no3z/ScratchTJ/software/player.h

/*
 * Copyright (C) 2018 Mark Hills <mark@xwax.org>
 *
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
 */

#ifndef PLAYER_H
#define PLAYER_H

#include <stdbool.h>
#include <stdio.h>
#include <stdlib.h>

#include "spin.h"
#include "track.h"

#define PLAYER_CHANNELS 2

// How many samples each beep stage lasts
#define BEEPSPEED 4800

#define BEEP_NONE -1
#define BEEP_RECORDINGSTART 0
#define BEEP_RECORDINGSTOP 1
#define BEEP_RECORDINGERROR 2




struct player {
    double sample_dt;

    spin lock;
    struct track *track;

    long samplesSoFar;


    /* Current playback parameters */

    double position, /* seconds */
        target_position, /* seconds, or TARGET_UNKNOWN */
        offset, /* track start point in timecode */
        last_difference, /* last known position minus target_position */
        pitch, /* from timecoder */
        sync_pitch, /* pitch required to sync to timecode signal */
        volume,
        note_pitch, // Pitch after note change
        fader_pitch, // pitch after fader change
        bend_pitch, // pitch after semitone bend change
		motor_speed; // speed of virtual motor, usually same as nominal_pitch but affected by start/stop

    /* Timecode control */

    struct timecoder *timecoder;
    bool timecode_control,
        recalibrate; /* re-sync offset at next opportunity */
	bool justPlay;
	double faderTarget; // Player should slowly fade to this level
	double faderVolume; // current fader volume
    double setVolume; // volume set by the volume controls on the back of the sc1000 or the volume buttons on the sc500 (or whatever over midi)
	bool capTouch;
	bool oldCapTouch;
	bool GoodToGo;
	bool stopped;

    bool recording;
    bool recordingStarted;

    int playingBeep;
    unsigned long beepPos;
    
    FILE *recordingFile;
    char recordingFileName[256];
};

void player_init(struct player *pl, unsigned int sample_rate,
                 struct track *track);
void player_clear(struct player *pl);
void player_set_volume(struct player *pl, int volume);

void player_set_timecode(struct player *pl, struct timecoder *tc);
void player_set_timecode_control(struct player *pl, bool on);
bool player_toggle_timecode_control(struct player *pl);
void player_set_internal_playback(struct player *pl);
 
void player_set_track(struct player *pl, struct track *track);
void player_clone(struct player *pl, const struct player *from);

double player_get_position(struct player *pl);
double player_get_elapsed(struct player *pl);
double player_get_remain(struct player *pl);
bool player_is_active(const struct player *pl);

void player_seek_to(struct player *pl, double seconds);
void player_recue(struct player *pl);

void player_collect(struct player *pl, signed short *pcm, unsigned samples);

#endif
