no3z/ScratchTJ/software/deck.h

/*
 * Copyright (C) 2018 Mark Hills <mark@xwax.org>
 *
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
 */

#ifndef DECK_H
#define DECK_H

#include <math.h>

#include "cues.h"
#include "device.h"
#include "player.h"
#include "realtime.h"
#include "sc_playlist.h"

#define NO_PUNCH (HUGE_VAL)

struct deck {
    struct device device;
    const char *importer;
    bool protect;

    struct player player;
    struct cues cues;

    /* Punch */

    double punch;

    /* A controller adds itself here */

    size_t ncontrol;
    struct controller *control[4];
	
	// If a shift modifier has been pressed recently
	bool shifted;

    struct Folder *FirstFolder, *CurrentFolder;
	struct File *CurrentFile;
    unsigned int NumFiles;
    bool filesPresent;

    int32_t angleOffset; // Offset between encoder angle and track position, reset every time the platter is touched
    int encoderAngle, newEncoderAngle ;
};

int deck_init(struct deck *deck, struct rt *rt,
              const char *importer,
              double speed, bool phono, bool protect, bool slave);
void deck_clear(struct deck *deck);

bool deck_is_locked(const struct deck *deck);
void load_track(struct deck *d, struct track *track);
void deck_recue(struct deck *deck);
void deck_clone(struct deck *deck, const struct deck *from);
void deck_unset_cue(struct deck *deck, unsigned int label);
void deck_cue(struct deck *deck, unsigned int label);
void deck_punch_in(struct deck *d, unsigned int label);
void deck_punch_out(struct deck *d);
void deck_load_folder(struct deck *d, char *FolderName);
void deck_next_file(struct deck *d);
void deck_prev_file(struct deck *d);
void deck_next_folder(struct deck *d);
void deck_prev_folder(struct deck *d);
void deck_random_file(struct deck *d);
void deck_record(struct deck *d);
#endif
